DrGlaucous/HeavyStringPlotter/CAD/STLs/ImobilePlotter/GondolaBase.stl

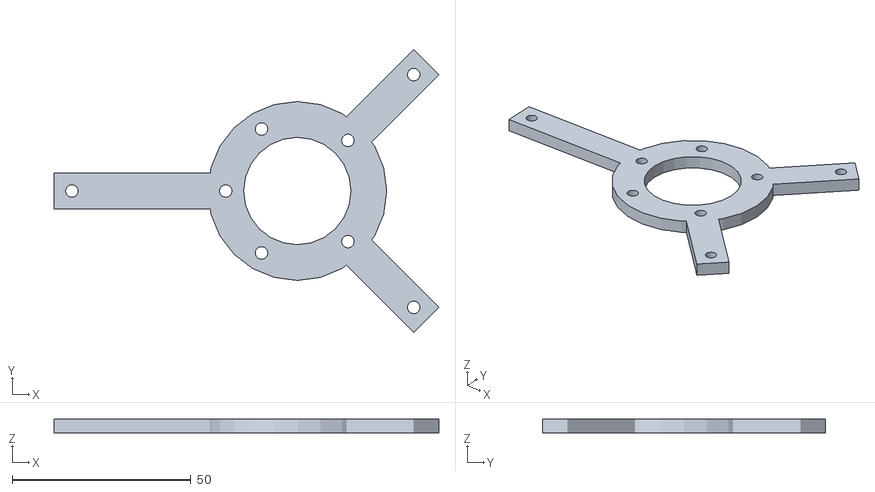
[picture p20: CAD file, 2023-03-16]
CAD/STLs/ImobilePlotter/GondolaBase.stl
107.6 x 79.2 x 4.00
