DrGlaucous/HeavyStringPlotter/CAD/STLs/MobilePlotter/ServoArm.stl

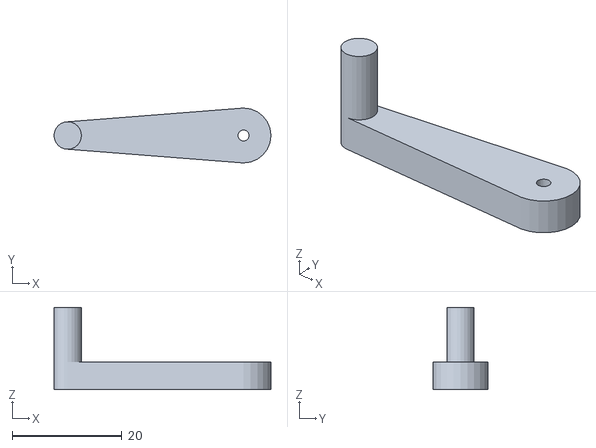
[picture p21: CAD file, 2023-02-22]
CAD/STLs/MobilePlotter/ServoArm.stl
39.5 x 10.0 x 15.0
