DrGlaucous/HeavyStringPlotter/CAD/STLs/ImobilePlotter/MarkerHolder.stl

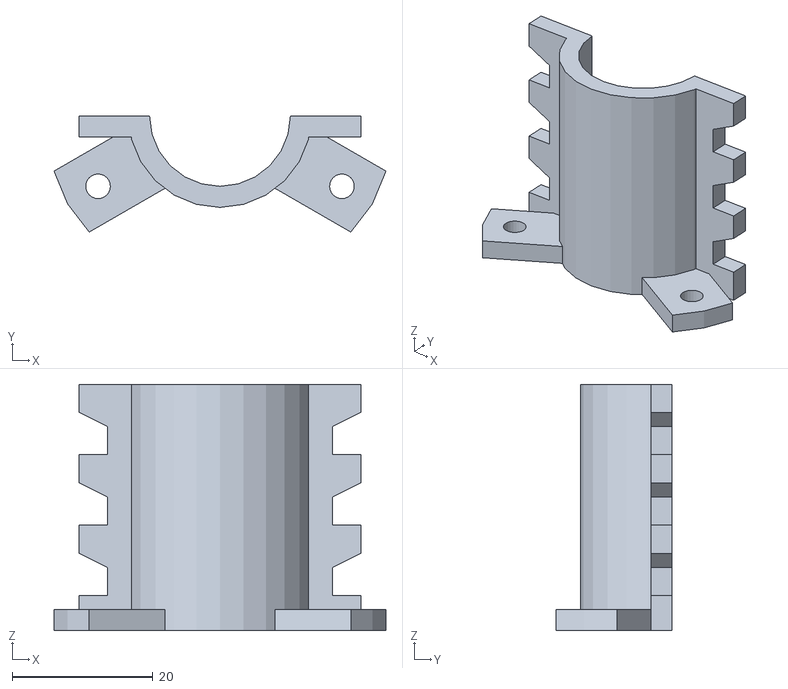
[picture p22: CAD file, 2023-03-16]
CAD/STLs/ImobilePlotter/MarkerHolder.stl
47.2 x 16.5 x 35.0
