DrGlaucous/HeavyStringPlotter/CAD/STLs/MobilePlotter/MountMarker.stl

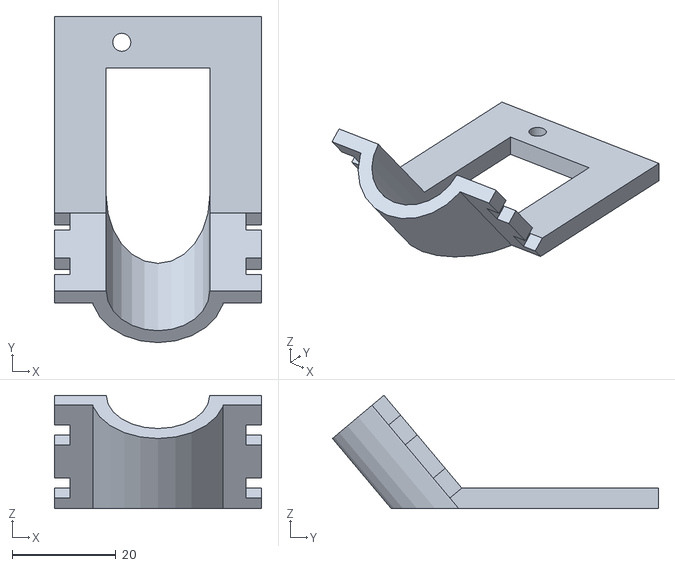
[picture p23: CAD file, 2023-02-22]
CAD/STLs/MobilePlotter/MountMarker.stl
40.0 x 63.0 x 21.9
