DrGlaucous/HeavyStringPlotter/CAD/STLs/ImobilePlotter/BatteryRest.stl

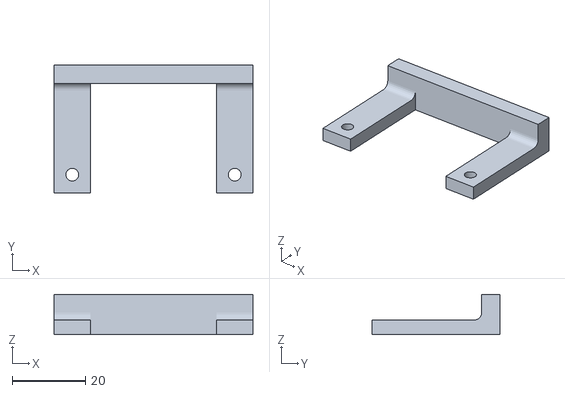
[picture p24: CAD file, 2023-03-16]
CAD/STLs/ImobilePlotter/BatteryRest.stl
54.5 x 35.0 x 11.0
