DrGlaucous/HeavyStringPlotter/CAD/STLs/MobilePlotter/MountServo.stl

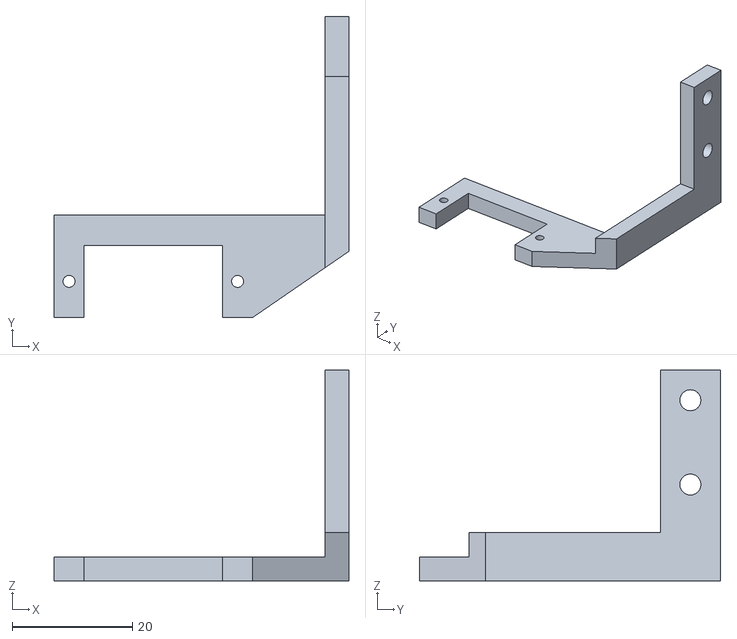
[picture p25: CAD file, 2023-02-22]
CAD/STLs/MobilePlotter/MountServo.stl
49.0 x 50.0 x 35.0
