DrGlaucous/HeavyStringPlotter/CAD/STLs/ImobilePlotter/GondolaHookLoop.stl

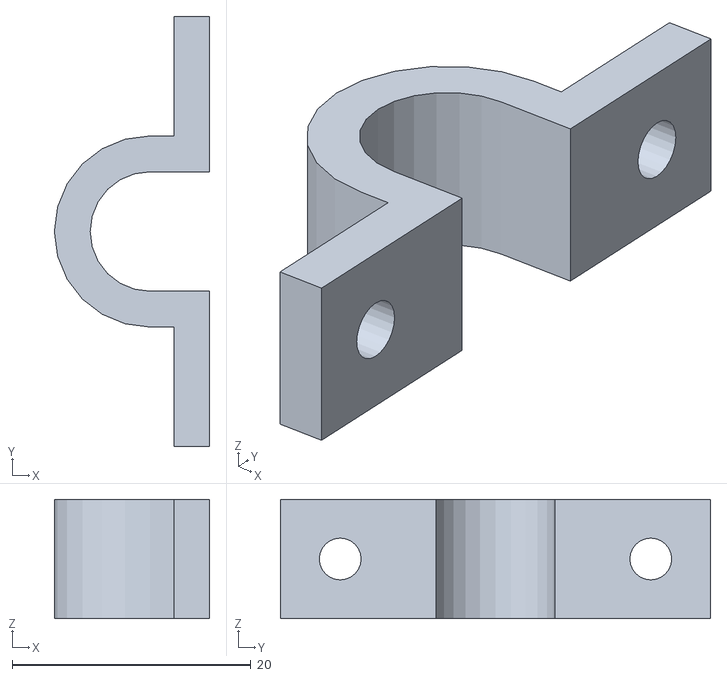
[picture p26: CAD file, 2023-03-16]
CAD/STLs/ImobilePlotter/GondolaHookLoop.stl
13.0 x 36.0 x 10.0
