DrGlaucous/HeavyStringPlotter/CAD/STLs/MobilePlotter/Base.stl

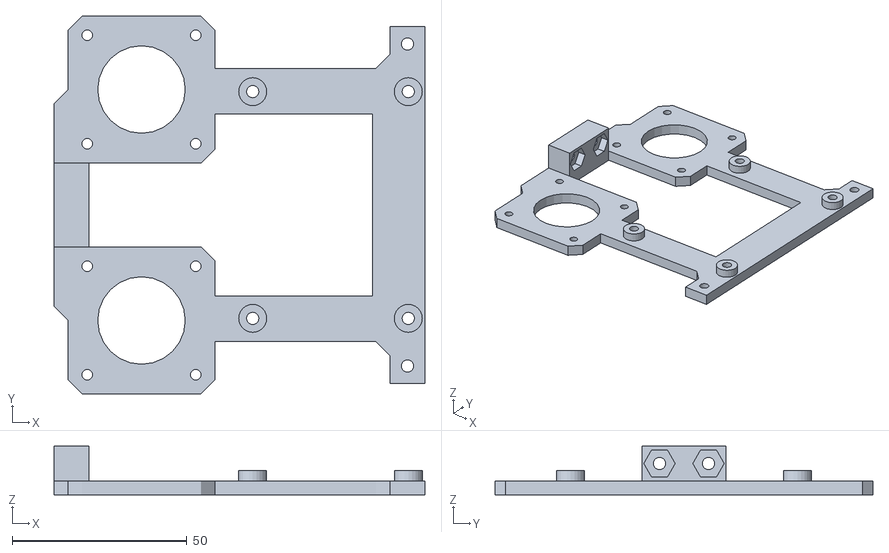
[picture p27: CAD file, 2023-02-22]
CAD/STLs/MobilePlotter/Base.stl
106.0 x 108.0 x 14.0
