DrGlaucous/HeavyStringPlotter/CAD/STLs/MobilePlotter/Pulley.stl

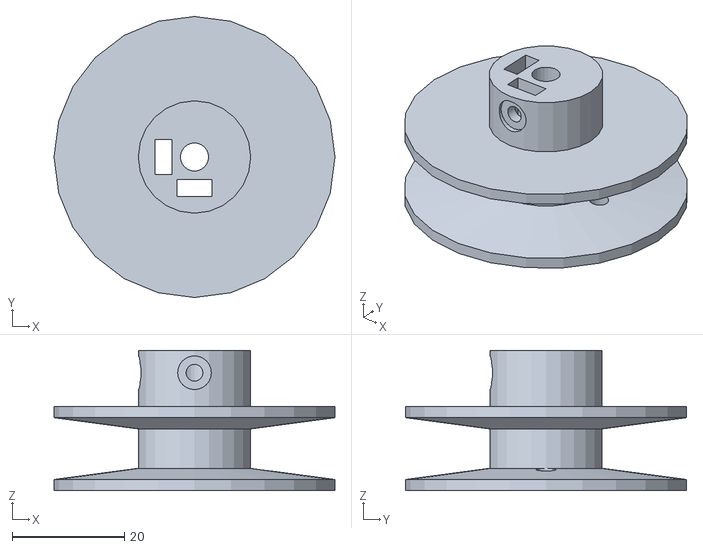
[picture p28: CAD file, 2023-02-22]
CAD/STLs/MobilePlotter/Pulley.stl
50.0 x 50.0 x 25.0
