DrGlaucous/HeavyStringPlotter/CAD/STLs/ImobilePlotter/CornerMotorBracket.stl

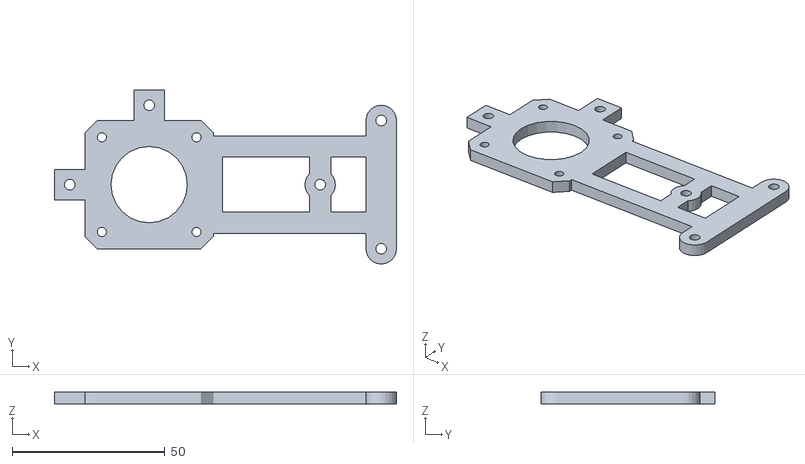
[picture p29: CAD file, 2023-03-16]
CAD/STLs/ImobilePlotter/CornerMotorBracket.stl
112.0 x 57.0 x 4.00
