DrGlaucous/HeavyStringPlotter/CAD/STLs/ImobilePlotter/ElectronicsBracket.stl

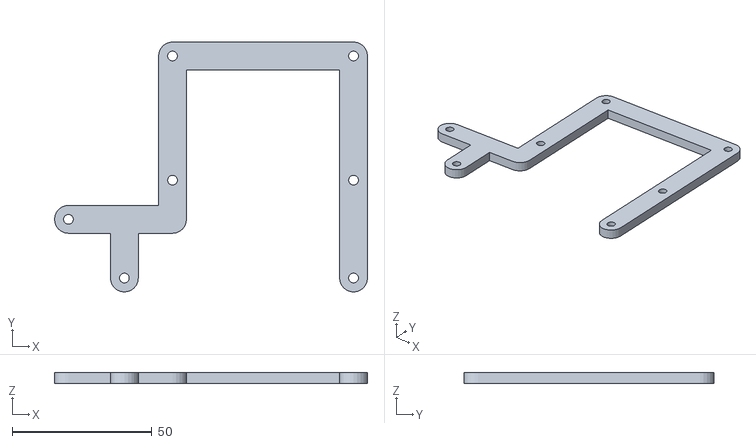
[picture p30: CAD file, 2023-03-16]
CAD/STLs/ImobilePlotter/ElectronicsBracket.stl
112.0 x 89.5 x 4.00
