DrGlaucous/HeavyStringPlotter/CAD/STLs/MobilePlotter/BackLeg.stl

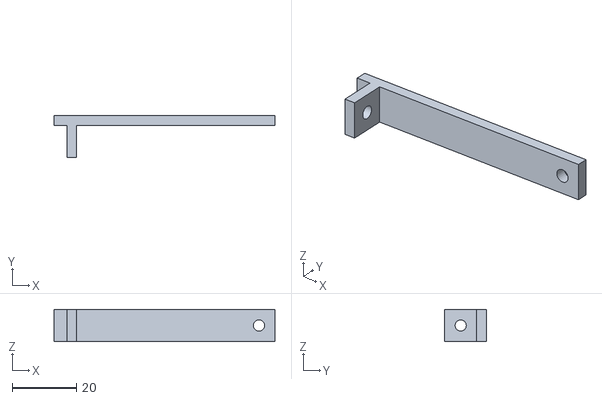
[picture p31: CAD file, 2023-02-22]
CAD/STLs/MobilePlotter/BackLeg.stl
69.0 x 13.0 x 10.0
