DrGlaucous/HeavyStringPlotter/CAD/STLs/ImobilePlotter/BracketSpacer.stl

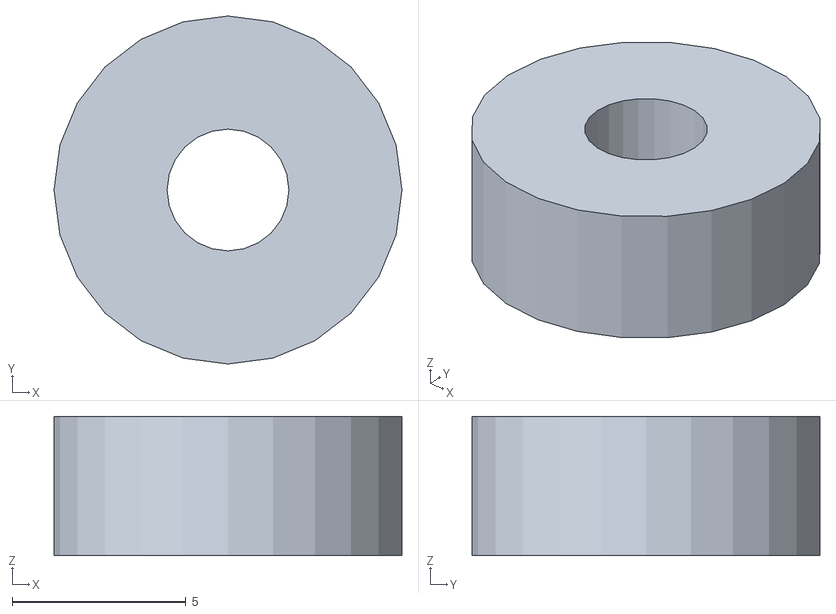
[picture p32: CAD file, 2023-03-16]
CAD/STLs/ImobilePlotter/BracketSpacer.stl
10.0 x 10.0 x 4.00
