DrGlaucous/HeavyStringPlotter/CAD/STLs/MobilePlotter/BatteryStrap.stl

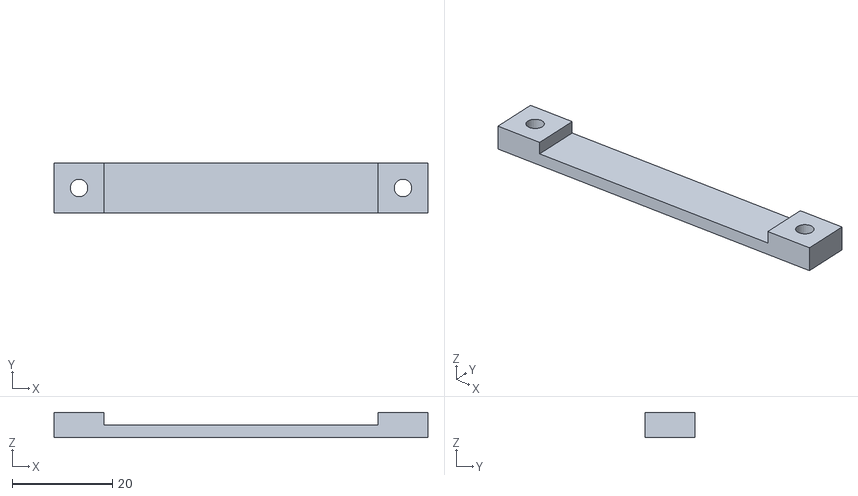
[picture p33: CAD file, 2023-02-22]
CAD/STLs/MobilePlotter/BatteryStrap.stl
74.8 x 10.0 x 5.00
