DrGlaucous/HeavyStringPlotter/CAD/STLs/ImobilePlotter/GondolaPartsKit.stl

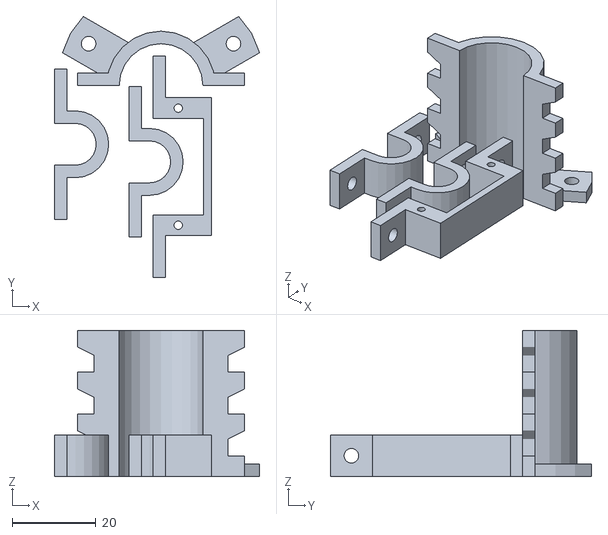
[picture p34: CAD file, 2023-03-16]
CAD/STLs/ImobilePlotter/GondolaPartsKit.stl
49.1 x 62.4 x 35.0
